ClusterM/fdskey/FdsKey/Core/Inc/sideselect.h

#ifndef INC_SIDESELECT_H_
#define INC_SIDESELECT_H_

#include "oled.h"
#include "ff.h"

#define SIDE_SELECT_GAME_NAME_FONT FONT_SLIMFONT_8
#define SIDE_SELECT_SIDE_NAME_FONT FONT_VERDANA_14_BOLD
#define SIDE_SELECT_HORIZONTAL_SCROLL_SPEED 2
#define SIDE_SELECT_HORIZONTAL_SCROLL_PAUSE 24

void fds_side_select(char *directory, FILINFO *fno, uint8_t load_first);
DotMatrixImage* side_select_get_disk_image(uint8_t side, uint8_t side_count);

#endif /* INC_SIDESELECT_H_ */
